defparam/21FX/photos/board_2.bmp

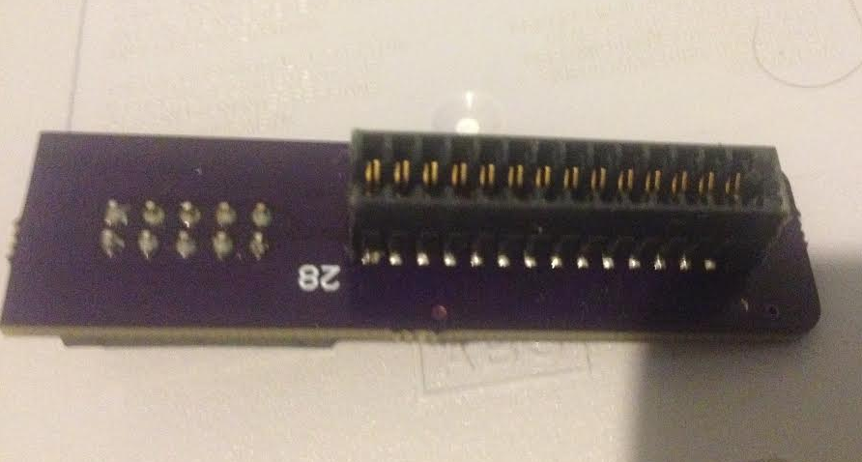
photos/board_2.bmp
