defparam/21FX/photos/board_3.bmp

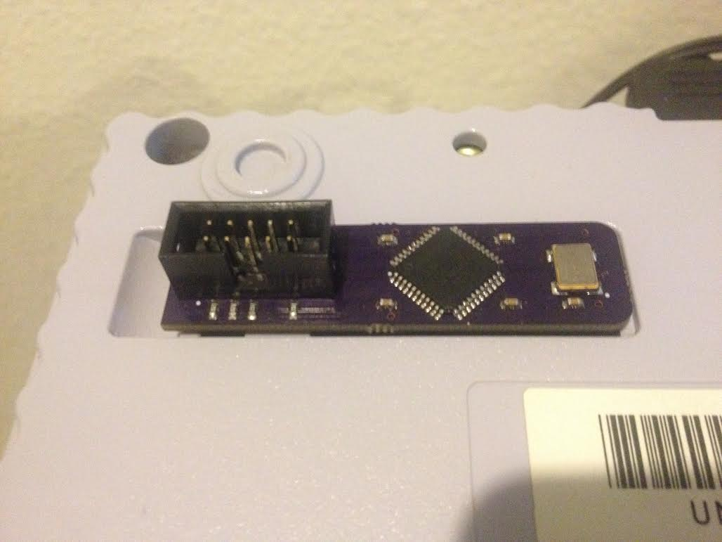
photos/board_3.bmp
