defparam/21FX/photos/sh_3dt2.png

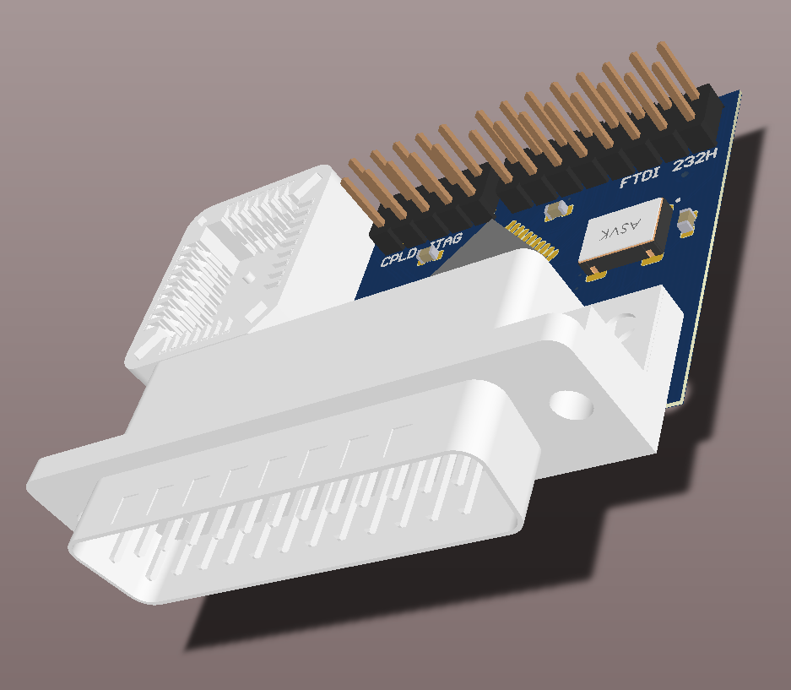
photos/sh_3dt2.png
